Sarahhan-one/Vib/SW_Vib/Vib_rev2/SW_files/Vib_Case_Silicon_rev2.SLDPRT

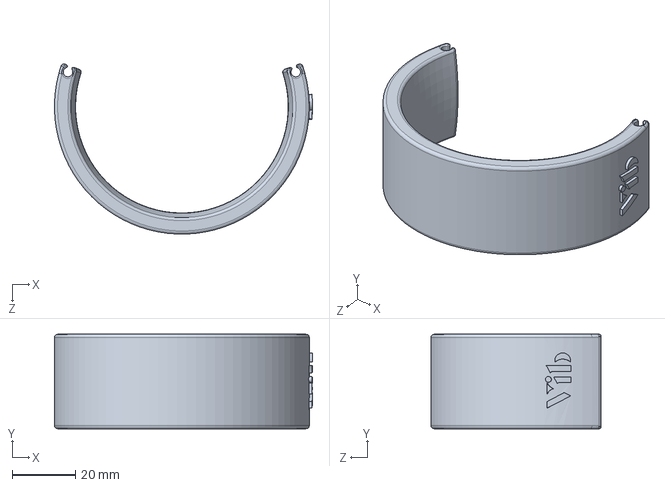
[picture p20: CAD file, 2024-10-01]
SW_Vib/Vib_rev2/SW_files/Vib_Case_Silicon_rev2.SLDPRT
81.9 x 30.0 x 54.0 mm
