Sarahhan-one/Vib/SW_Vib/Vib_rev2/SW_files/NoBuckleStrap_Silicon_flatten.SLDPRT

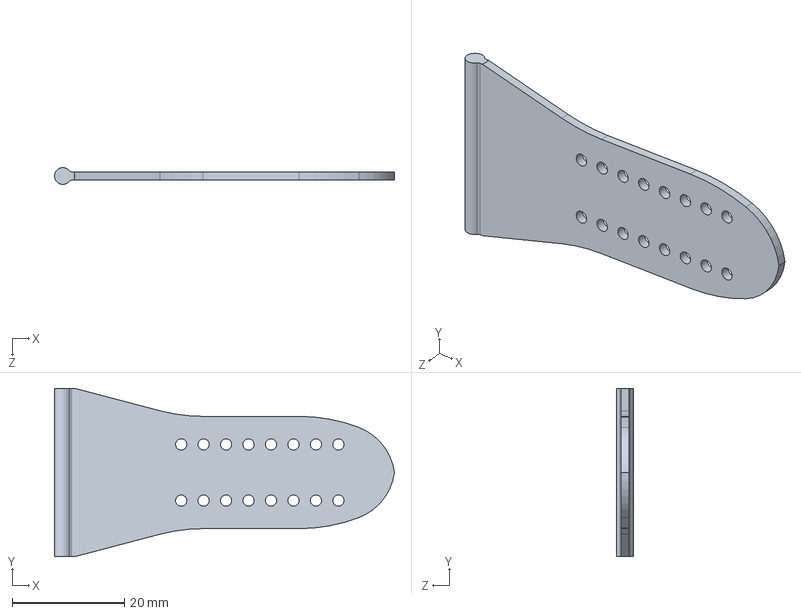
[picture p21: CAD file, 2024-10-01]
SW_Vib/Vib_rev2/SW_files/NoBuckleStrap_Silicon_flatten.SLDPRT
60.6 x 30.0 x 2.98 mm
