Sarahhan-one/Vib/SW_Vib/Vib_printing/Vib_printing_SW/Vib_Case_printing.SLDPRT

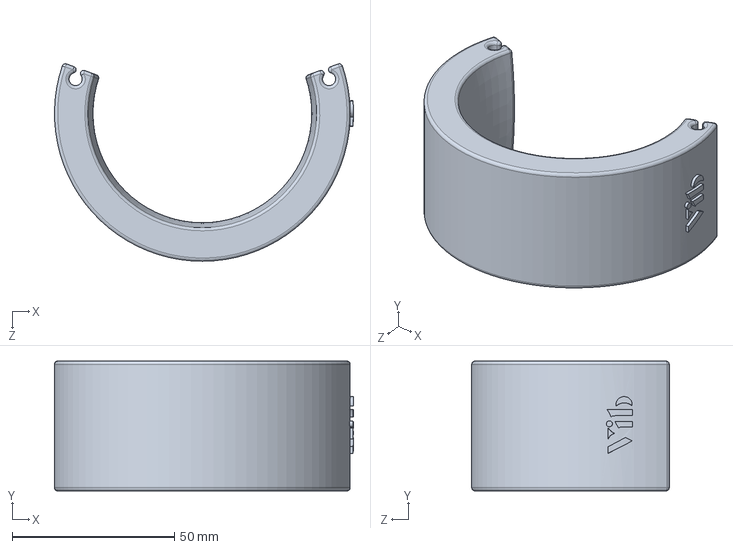
[picture p22: CAD file, 2024-10-01]
SW_Vib/Vib_printing/Vib_printing_SW/Vib_Case_printing.SLDPRT
92.0 x 40.0 x 60.8 mm
